levon-m/bassmint/hardware/schematics/bassmint.kicad_sch

## KiCad design hardware/schematics/bassmint.kicad_sch (2025-12-10)

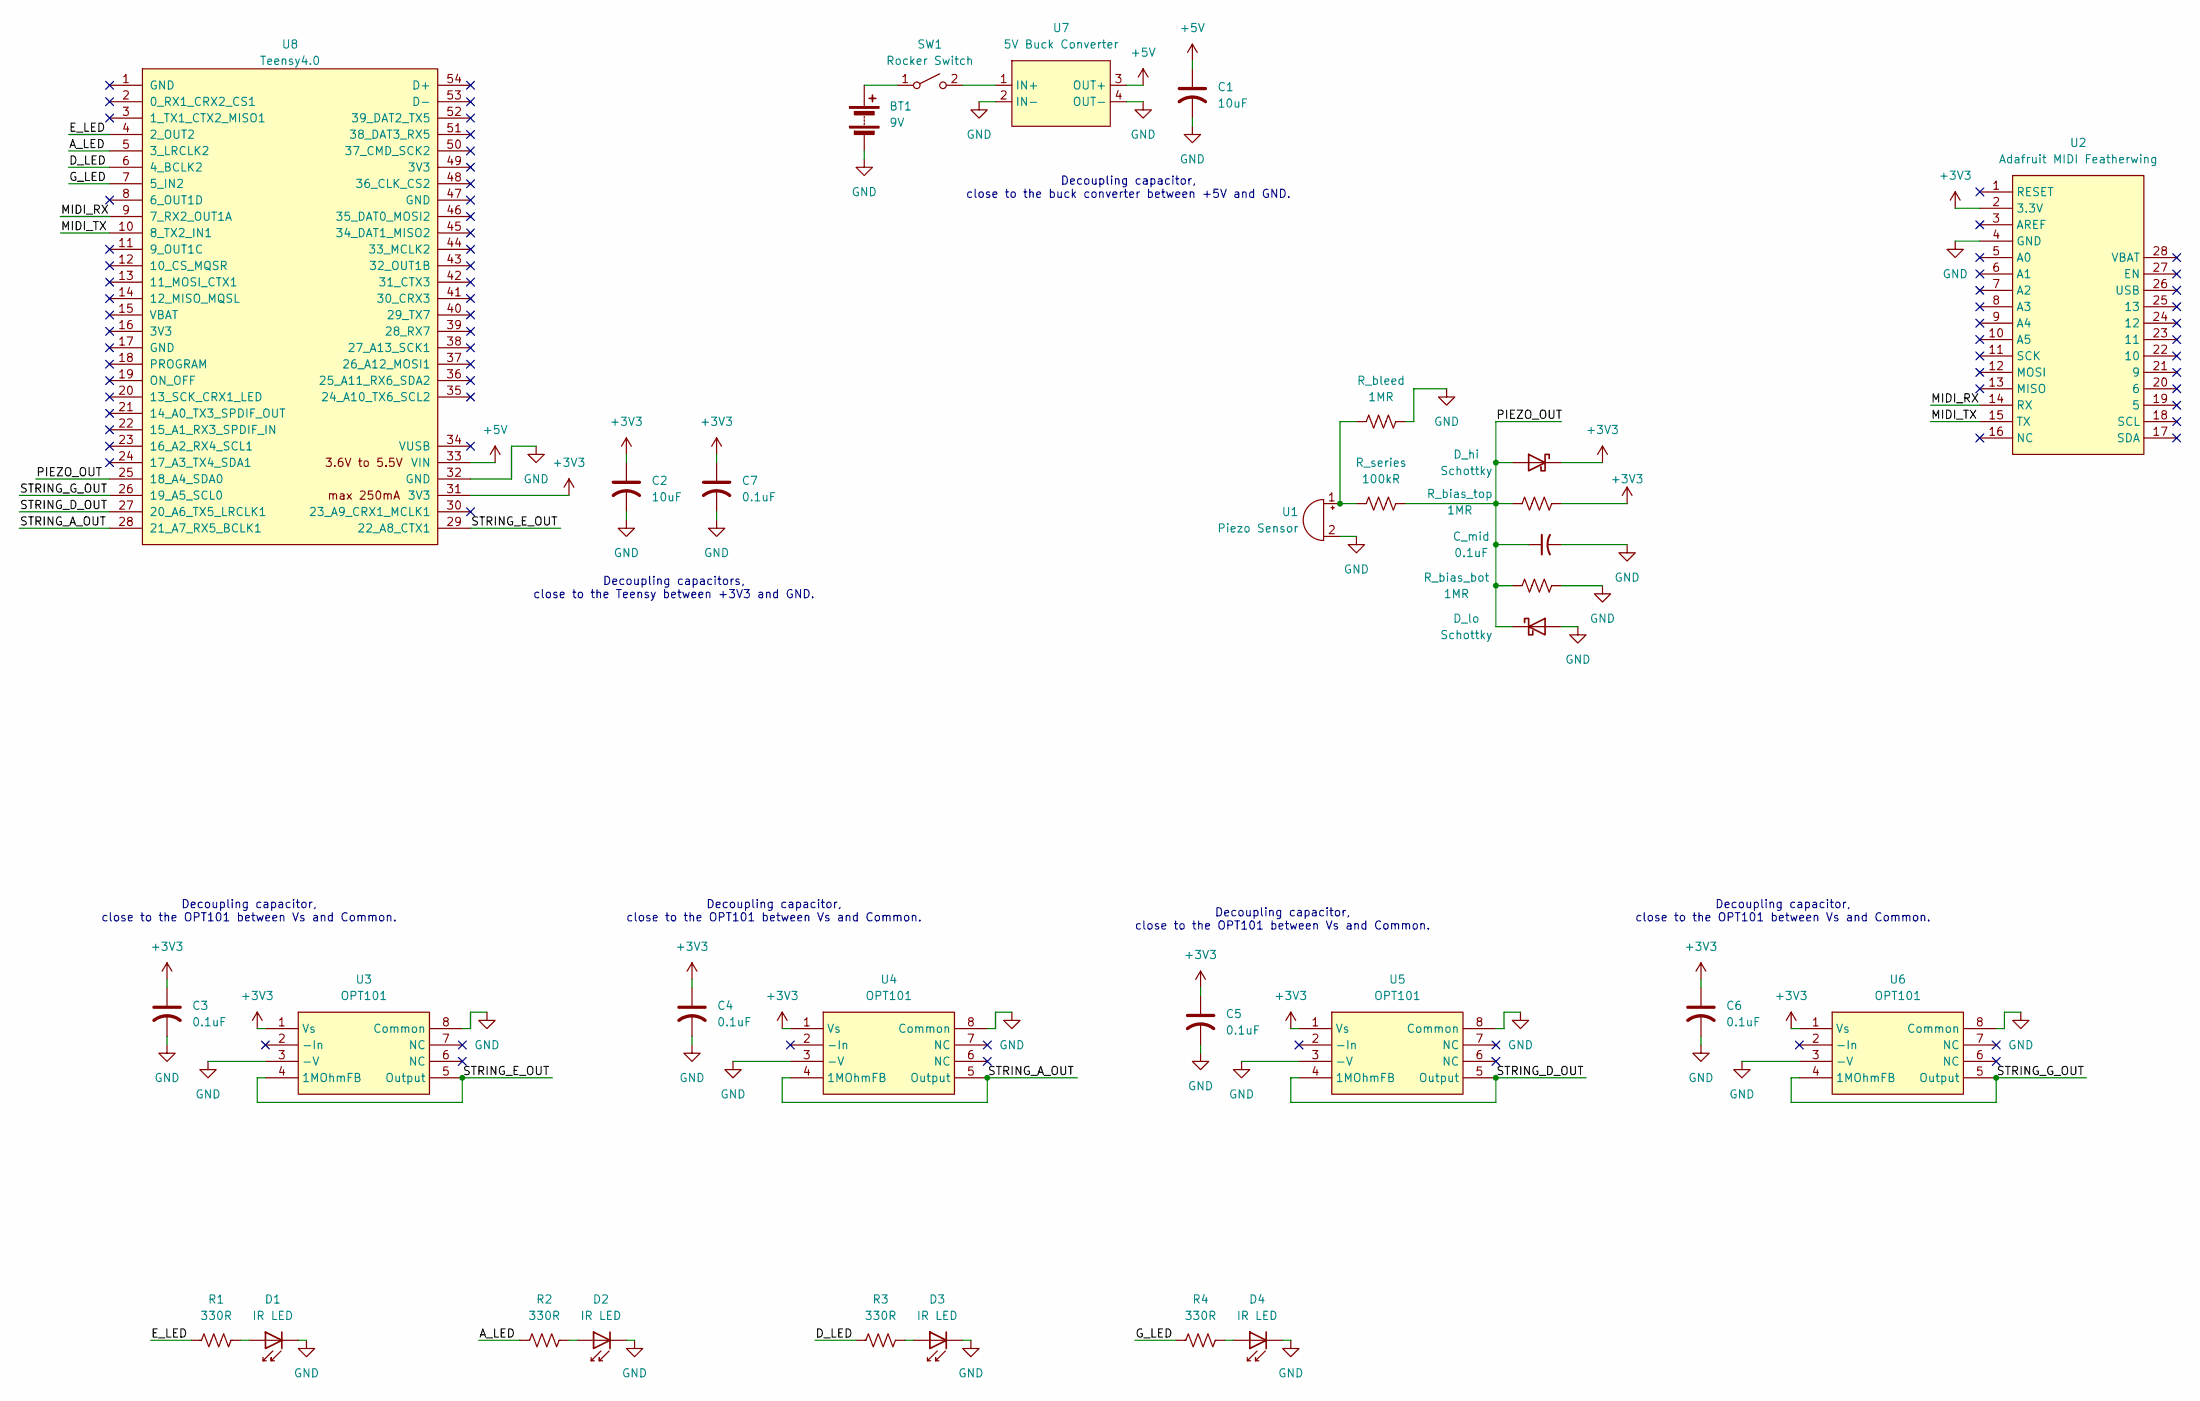
[picture p2: schematic bassmint.kicad_sch]

Parts:
BT1: 9V
C1, C2: 10uF
C3, C4, C5, C6, C7: 0.1uF
C_mid: 0.1uF
D1, D2, D3, D4: IR LED; LED_D5.0mm_IRGrey
D_hi: Schottky; D_DO-41_SOD81_P10.16mm_Horizontal
D_lo: Schottky; D_DO-41_SOD81_P10.16mm_Horizontal
R1, R2, R3, R4: 330R
R_bias_bot: 1MR
R_bias_top: 1MR
R_bleed: 1MR
R_series: 100kR
SW1: Rocker Switch
U1: Piezo Sensor
U2: Adafruit MIDI Featherwing
U3, U4, U5, U6: OPT101
U7: 5V Buck Converter
U8: Teensy4.0

Connections:
+3V3: C2.1, C3.1, C4.1, C5.1, C6.1, C7.1, D_hi.1 (K), R_bias_top.2, U2.2 (3.3V), U3.1 (Vs), U4.1 (Vs), U5.1 (Vs), U6.1 (Vs), U8.31 (3V3)
+5V: C1.1, U7.3 (OUT+), U8.33 (VIN)
A_LED: R2.2, U8.5 (3_LRCLK2)
D_LED: R3.2, U8.6 (4_BCLK2)
E_LED: R1.2, U8.4 (2_OUT2)
GND: BT1.2 (-), C1.2, C2.2, C3.2, C4.2, C5.2, C6.2, C7.2, C_mid.2, D1.1 (K), D2.1 (K), D3.1 (K), D4.1 (K), D_lo.2 (A), R_bias_bot.2, R_bleed.2, U1.2 (-), U2.4 (GND), U3.3 (-V), U3.8 (Common), U4.3 (-V), U4.8 (Common), U5.3 (-V), U5.8 (Common), U6.3 (-V), U6.8 (Common), U7.2 (IN-), U7.4 (OUT-), U8.32 (GND)
G_LED: R4.2, U8.7 (5_IN2)
MIDI_RX: U2.14 (RX), U8.9 (7_RX2_OUT1A)
MIDI_TX: U2.15 (TX), U8.10 (8_TX2_IN1)
unnamed: BT1.1 (+), SW1.1 (A)
unnamed: D1.2 (A), R1.1
unnamed: D2.2 (A), R2.1
unnamed: D3.2 (A), R3.1
unnamed: D4.2 (A), R4.1
unnamed: R_bleed.1, R_series.1, U1.1 (+)
unnamed: SW1.2 (B), U7.1 (IN+)
PIEZO_OUT: C_mid.1, D_hi.2 (A), D_lo.1 (K), R_bias_bot.1, R_bias_top.1, R_series.2, U8.25 (18_A4_SDA0)
STRING_A_OUT: U4.4 (1MOhmFB), U4.5 (Output), U8.28 (21_A7_RX5_BCLK1)
STRING_D_OUT: U5.4 (1MOhmFB), U5.5 (Output), U8.27 (20_A6_TX5_LRCLK1)
STRING_E_OUT: U3.4 (1MOhmFB), U3.5 (Output), U8.29 (22_A8_CTX1)
STRING_G_OUT: U6.4 (1MOhmFB), U6.5 (Output), U8.26 (19_A5_SCL0)

Notes on the sheet:
Decoupling capacitor, close to the OPT101 between Vs and Common.
Decoupling capacitors, close to the Teensy between +3V3 and GND.
Decoupling capacitor, close to the buck converter between +5V and GND.
